birdybro/MiSTer-Barcade/3d Printed Parts/Decorations/Other/Pacman_Plate.stl

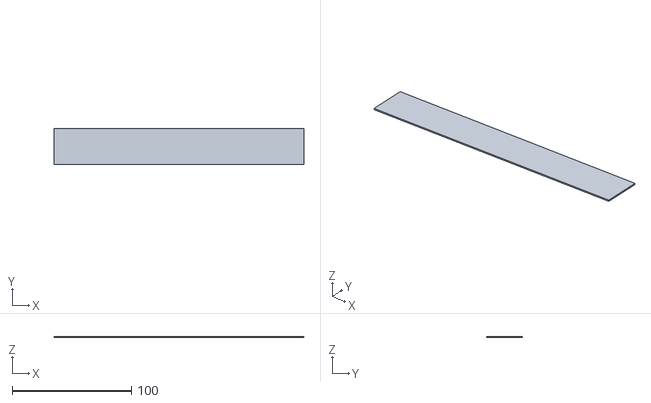
[picture p20: CAD file, 2021-05-28]
3d Printed Parts/Decorations/Other/Pacman_Plate.stl
210.0 x 30.0 x 1.00
