birdybro/MiSTer-Barcade/3d Printed Parts/Arcade Cabinet/Mini_Arcade_10_buttons.stl

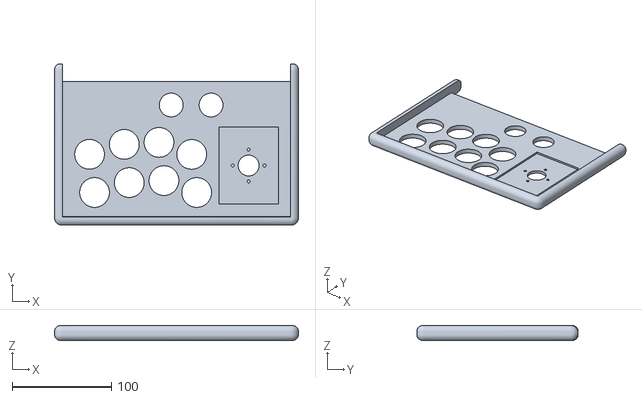
[picture p21: CAD file, 2021-05-28]
3d Printed Parts/Arcade Cabinet/Mini_Arcade_10_buttons.stl
246.0 x 162.8 x 15.0
