birdybro/MiSTer-Barcade/3d Printed Parts/Decorations/Other/Pacman_dot.stl

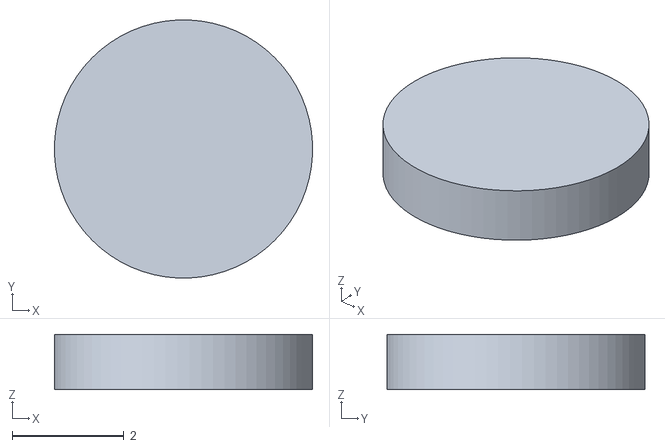
[picture p22: CAD file, 2021-05-28]
3d Printed Parts/Decorations/Other/Pacman_dot.stl
4.62 x 4.62 x 0.99
