birdybro/MiSTer-Barcade/3d Printed Parts/Arcade Cabinet/Rubber_foot.stl

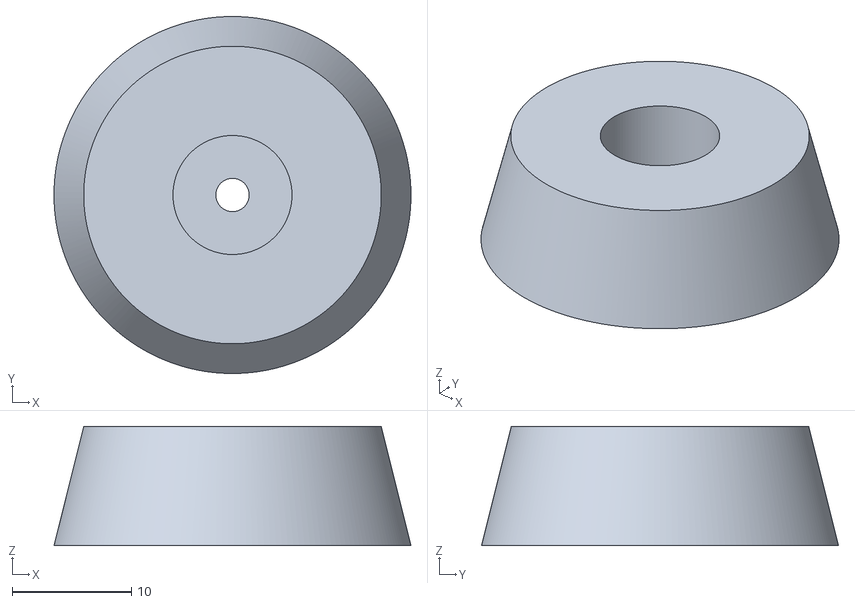
[picture p23: CAD file, 2021-05-28]
3d Printed Parts/Arcade Cabinet/Rubber_foot.stl
30.0 x 30.0 x 10.0
