birdybro/MiSTer-Barcade/3d Printed Parts/Decorations/Other/Mister_Genesis_Logo_Text.stl

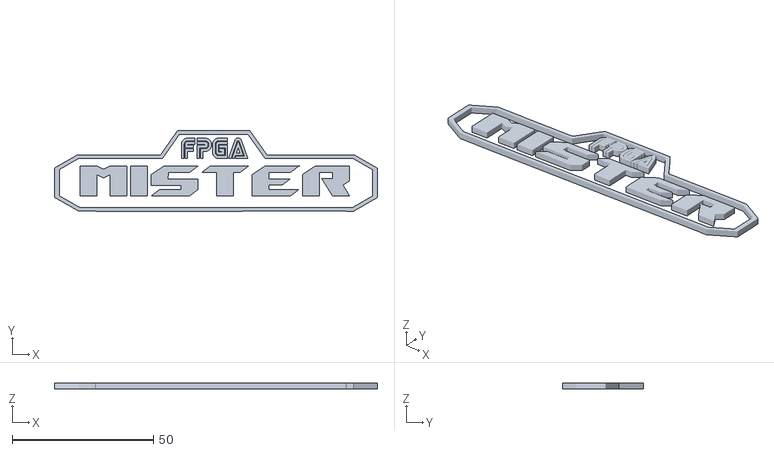
[picture p24: CAD file, 2021-05-28]
3d Printed Parts/Decorations/Other/Mister_Genesis_Logo_Text.stl
114.5 x 28.6 x 2.00
